JackGamerCYT/IOT-PROJECT3-/docs/PINOUT.xlsx

Sheet: Pinout
STT | Linh kiện | Chân linh kiện | Chân ESP32-S3 / mạch | Loại tín hiệu | Chức năng
1 | ACS712-05B | VCC | 5V (sau LM2596) | Nguồn DC | Nguồn nuôi cảm biến cách ly
2 | ACS712-05B | GND | GND chung | Mass
3 | ACS712-05B | OUT | GPIO 1 (ADC1_CH0) qua phân áp 10k/20k | Analog in | Đo dòng tải DC, 185 mV/A
4 | Relay 2CH 5V | VCC / JD-VCC | 3.3V / 5V | Nguồn | Tháo jumper để 3.3V tắt hẳn opto
5 | Relay 2CH 5V | IN1 | GPIO 12 | Digital out | Tải 1 – Quạt 12V (ưu tiên cao)
6 | Relay 2CH 5V | IN2 | GPIO 13 | Digital out | Tải 2 – LED 12V (ưu tiên thấp)
7 | DS3231 (0x68) | VCC/GND/SDA/SCL | 3V3/GND/GPIO 8/GPIO 9 | I2C | Giữ giờ khi mất WiFi
8 | SSD1306 (0x3C) | VCC/GND/SDA/SCL | 3V3/GND/GPIO 8/GPIO 9 | I2C | Hiển thị tại chỗ
9 | Buzzer 5V + S8050 | Base qua R 1k | GPIO 14 | Digital out | Báo động vượt ngưỡng
10 | LM2596 | IN+ / IN- | Domino 12V sau cầu chì | Power in
11 | LM2596 | OUT+ / OUT- | 5V / GND ESP32 | Power out | Chỉnh 5.00 V trước khi cắm chip

Sheet: Mach dong luc
Tải / thiết bị | Nguồn +12V | Qua relay | Qua ACS712 | Nguồn -12V | Khi kích LOW
Tải 1: Quạt DC 12V | +12V sau cầu chì 2A | COM1 → NO1 | IP+ → IP- (đo chung) | GND 12V | Quạt chạy
Tải 2: LED 12V | +12V sau cầu chì 2A | COM2 → NO2 | IP+ → IP- (đo chung) | GND 12V | Đèn sáng
LM2596 | +12V trực tiếp | Không | Không qua (để không tính vào phép đo) | GND 12V | Ra 5V liên tục
Diode 1N4007 | Catot vào (+) quạt |  |  | Anot vào (-) quạt | Triệt sức điện động ngược

Sheet: Linh kien
STT | Tên linh kiện | SL | Đơn giá (đ) | Thành tiền (đ) | Ghi chú
1 | ESP32-S3 DevKitC N16R8 | 1 | 180000 |  | Không dùng ESP32 classic vì GPIO12 là chân strapping
2 | Cảm biến dòng ACS712-05B | 1 | 45000
3 | Module relay 2 kênh 5V | 1 | 30000 |  | Active low, 10A/30VDC
4 | Mạch hạ áp LM2596 | 1 | 22000
5 | DS3231 RTC | 1 | 35000 |  | Kèm pin CR2032
6 | OLED SSD1306 0.96" | 1 | 45000 |  | I2C 0x3C
7 | Quạt DC 12V | 1 | 25000 |  | Tải ưu tiên cao
8 | Đèn LED bar 12V | 1 | 20000 |  | Tải ưu tiên thấp
9 | Adapter 12V 2A | 1 | 65000
10 | Phíp lỗ 7x9cm + domino + rào cái | 1 | 40000
11 | Cầu chì 2A + đế, diode 1N4007, R 10k/20k | 1 | 20000 |  | Bảo vệ và phân áp ADC
12 | Buzzer 5V + S8050 + R 1k | 1 | 10000 |  | Tuỳ chọn
13 | Thiếc hàn + flux | 1 | 35000
 | TỔNG
