JackGamerCYT/IOT-PROJECT3-/firmware/esp32_firmware/secrets.h

// ============================================================================
//  secrets.h  -  thong tin rieng, KHONG commit len GitHub
//  File nay da nam trong .gitignore cua du an.
//  Dat canh file esp32_firmware.ino (cung thu muc) roi nap lai chuong trinh.
// ============================================================================
#pragma once

#define WIFI_SSID     "HO TRO SINH VIEN"
#define WIFI_PASSWORD "12345678@"

// Broker HiveMQ cong khai khong can tai khoan -> de trong
#define MQTT_USER     ""
#define MQTT_PASS     ""
