JackGamerCYT/IOT-PROJECT3-/firmware/esp32_firmware/secrets.example.h

// Copy file này thành secrets.h (cùng thư mục .ino) và điền thông tin. KHÔNG commit secrets.h.
#pragma once
#define WIFI_SSID     "YOUR_WIFI"
#define WIFI_PASSWORD "YOUR_PASSWORD"
#define MQTT_USER     ""   // để trống khi dùng broker.hivemq.com public
#define MQTT_PASS     ""
